Gingernut08/Action-Cam/Schematic/Action Cam.kicad_sch

## KiCad design Schematic/Action Cam.kicad_sch (2026-02-06)

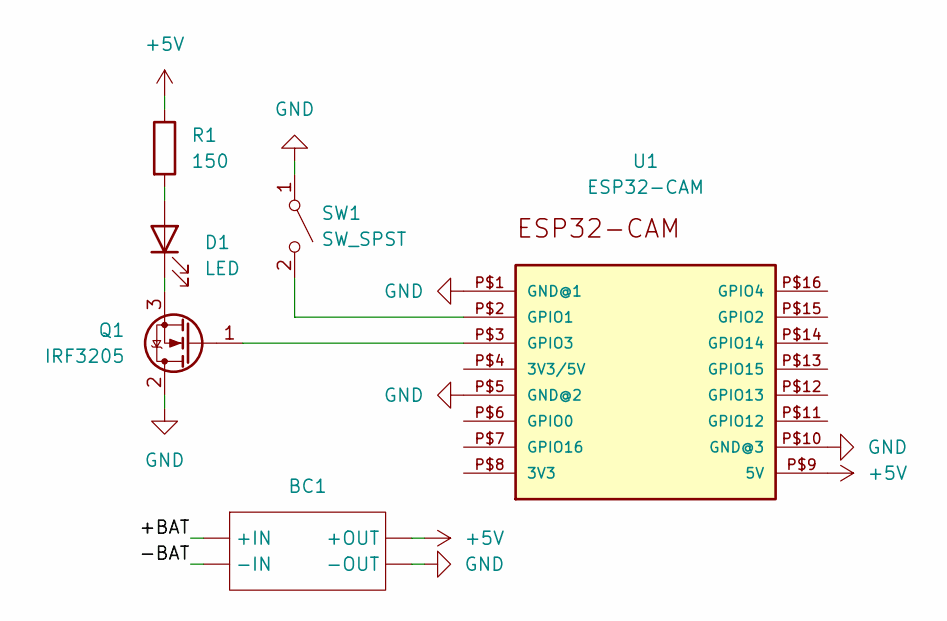
[picture p5: schematic Action Cam.kicad_sch]

Parts:
BC1: (no value)
D1: LED
Q1: IRF3205; TO-220-3_Vertical
R1: 150
SW1: SW_SPST
U1: ESP32-CAM

Connections:
+5V: BC1., R1.1, U1.P$9 (5V)
+BAT: BC1.
-BAT: BC1.
GND: BC1., Q1.2 (D), SW1.1 (A), U1.P$1 (GND@1), U1.P$5 (GND@2), U1.P$10 (GND@3)
unnamed: D1.1 (K), Q1.3 (S)
unnamed: D1.2 (A), R1.2
unnamed: Q1.1 (G), U1.P$3 (GPIO3)
unnamed: SW1.2 (B), U1.P$2 (GPIO1)
